MrCybernetic/FSL_ScanLess/img/montre.png

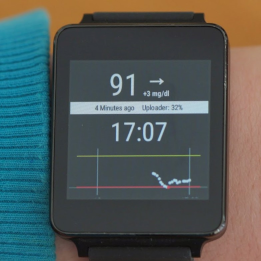
img/montre.png
