MrCybernetic/FSL_ScanLess/SCANLESS/img/Enclosure2.png

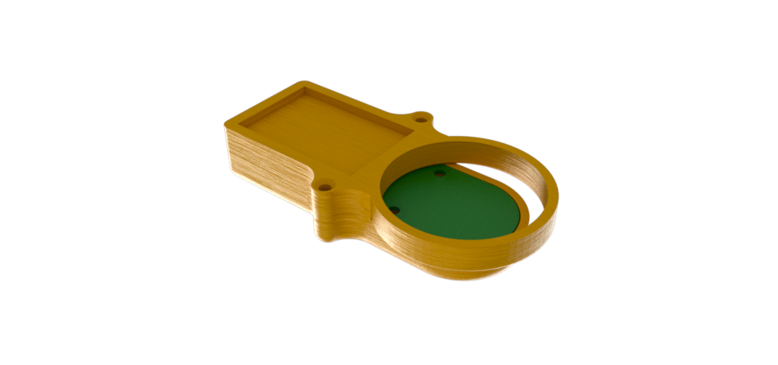
SCANLESS/img/Enclosure2.png
