MrCybernetic/FSL_ScanLess/SCANLESS/img/full2.jpg

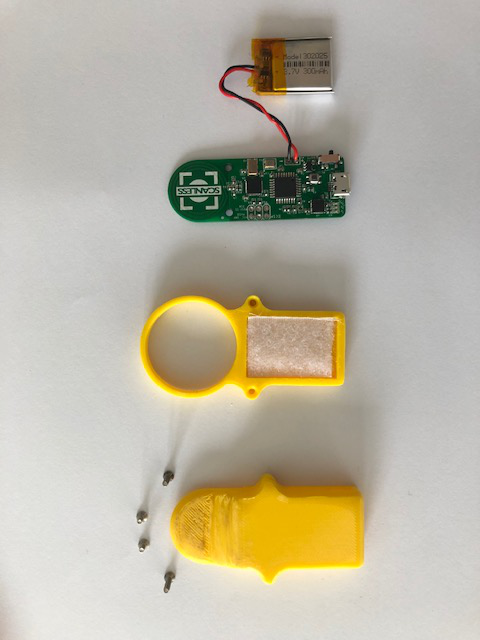
SCANLESS/img/full2.jpg
