MrCybernetic/FSL_ScanLess/SCANLESS/img/full.jpg

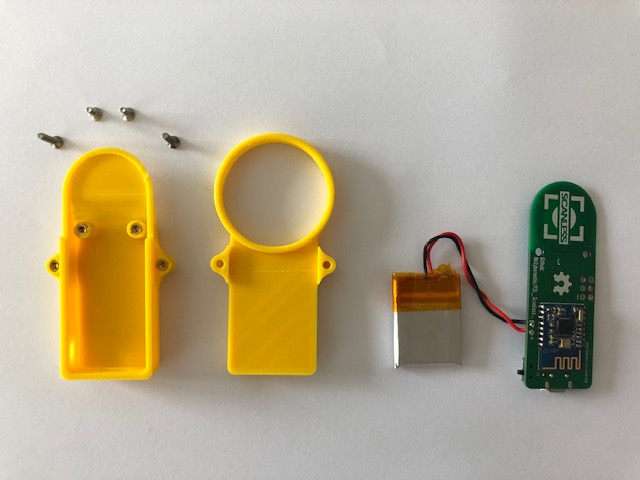
SCANLESS/img/full.jpg
