MrCybernetic/FSL_ScanLess/SCANLESS/img/PCB2.jpg

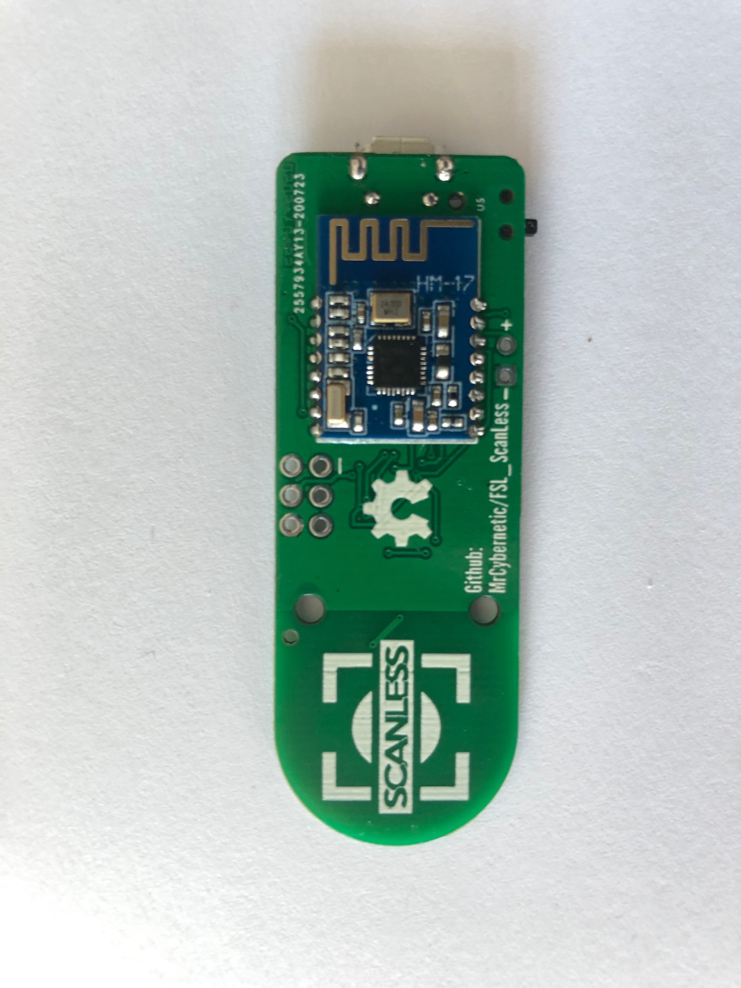
SCANLESS/img/PCB2.jpg
