MrCybernetic/FSL_ScanLess/SCANLESS/img/PCB.jpg

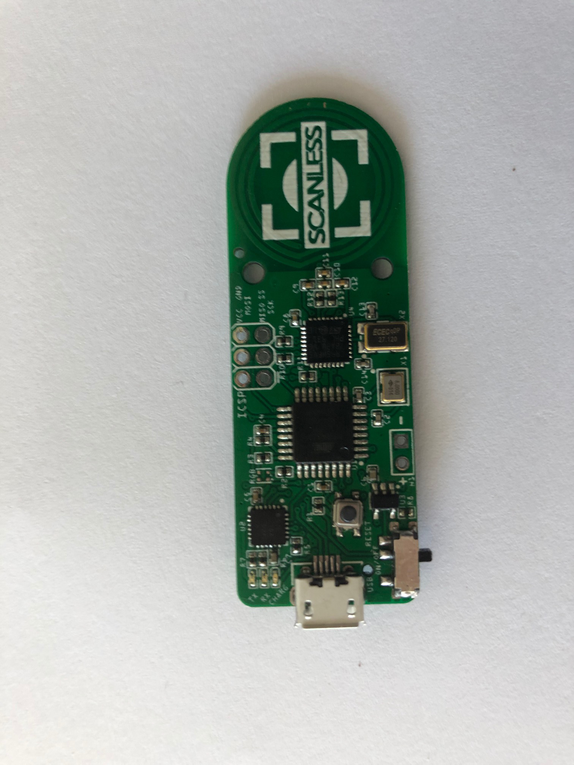
SCANLESS/img/PCB.jpg
