MrCybernetic/FSL_ScanLess/SCANLESS/img/PCBBattery2.jpg

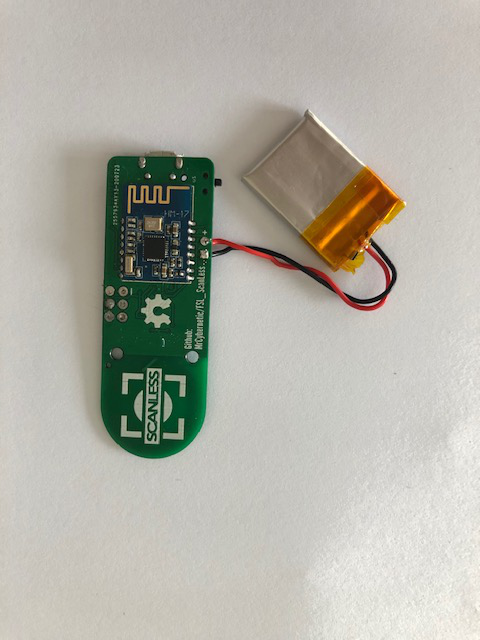
SCANLESS/img/PCBBattery2.jpg
