MrCybernetic/FSL_ScanLess/SCANLESS/img/PCBBattery.jpg

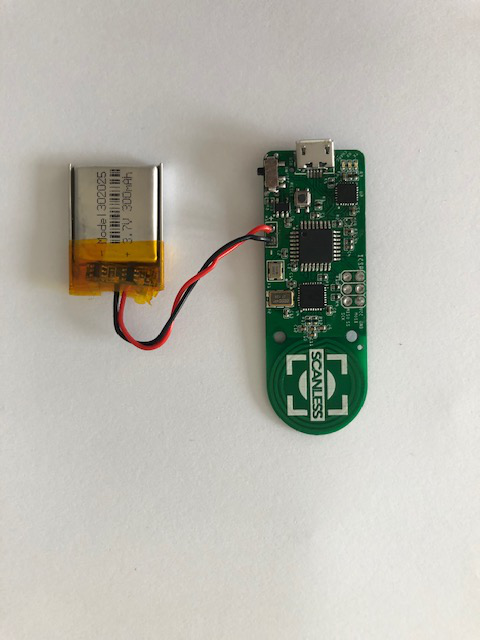
SCANLESS/img/PCBBattery.jpg
